1502Pam/Project/Imágenes/2B.png

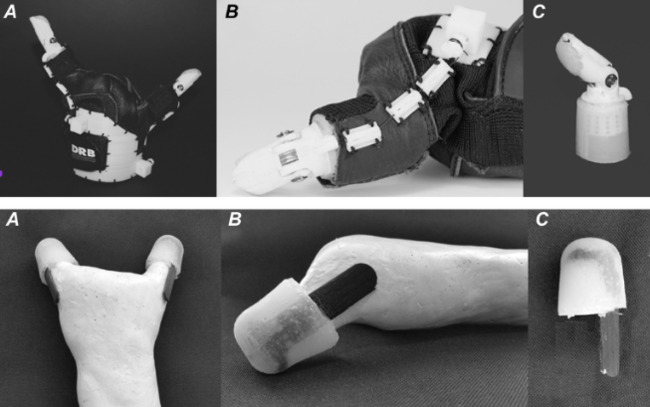
Imágenes/2B.png
