1502Pam/Project/Imágenes/1M_n.jpeg

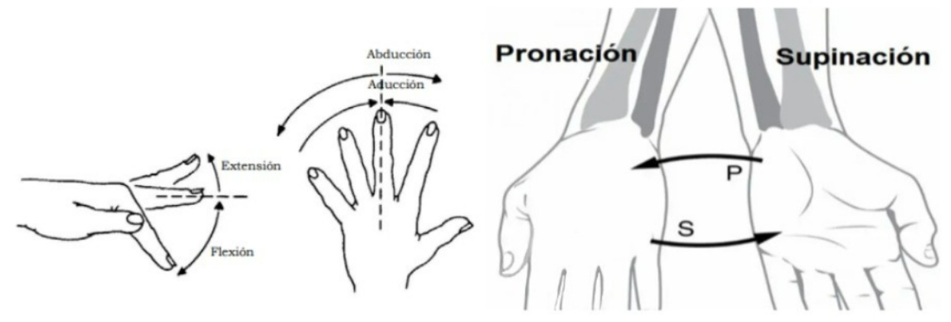
Imágenes/1M_n.jpeg
