1502Pam/Project/Imágenes/1S.jpg

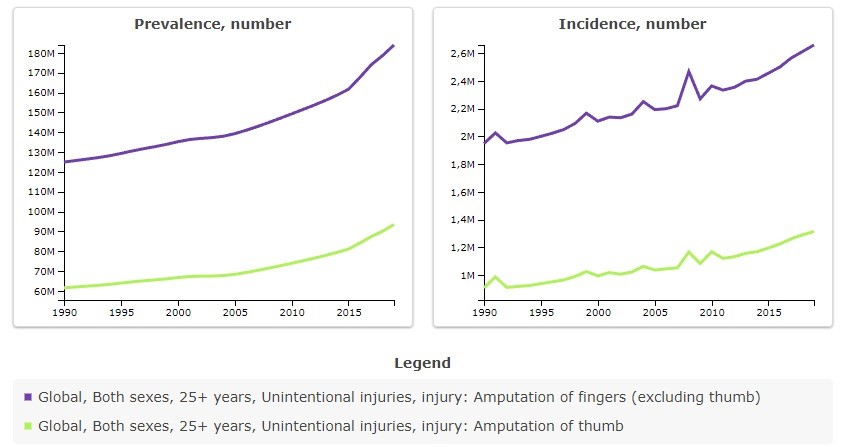
Imágenes/1S.jpg
