1502Pam/Project/Imágenes/3M_n.jpeg

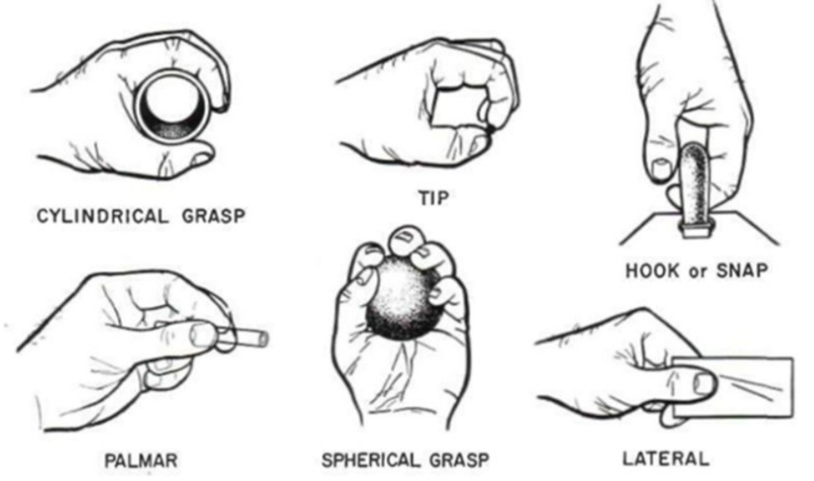
Imágenes/3M_n.jpeg
