1502Pam/Project/Imágenes/4B.png

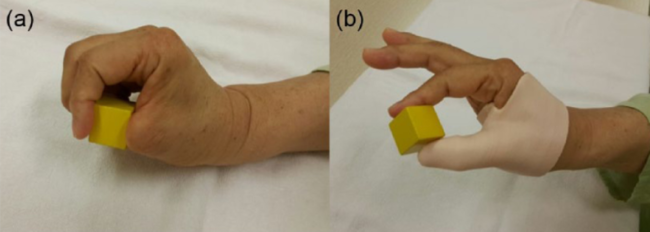
Imágenes/4B.png
