1502Pam/Project/Imágenes/10_2023-08-31 125352.jpg

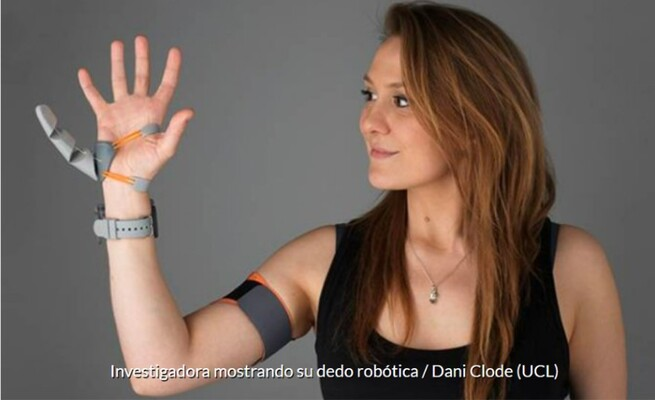
Imágenes/10_2023-08-31 125352.jpg
