1502Pam/Project/Imágenes/B1.png

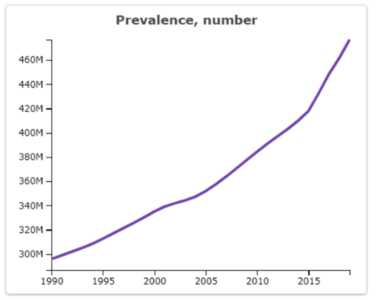
Imágenes/B1.png
