1502Pam/Project/Imágenes/B2.png

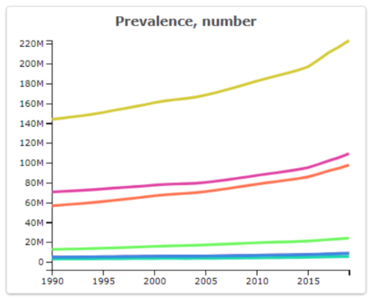
Imágenes/B2.png
