1502Pam/Project/Imágenes/B3.png

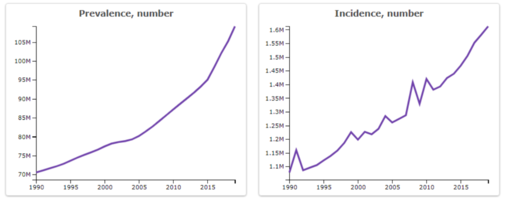
Imágenes/B3.png
