1502Pam/Project/Imágenes/B5.png

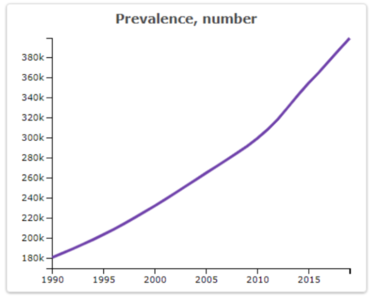
Imágenes/B5.png
