1502Pam/Project/Imágenes/boceto3.1.jpg

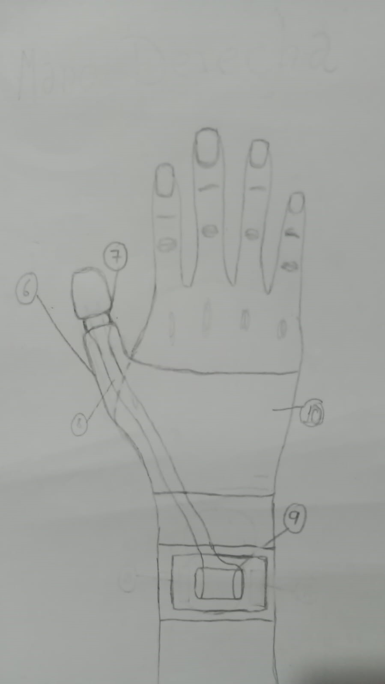
Imágenes/boceto3.1.jpg
