1502Pam/Project/Imágenes/boceto3.jpg

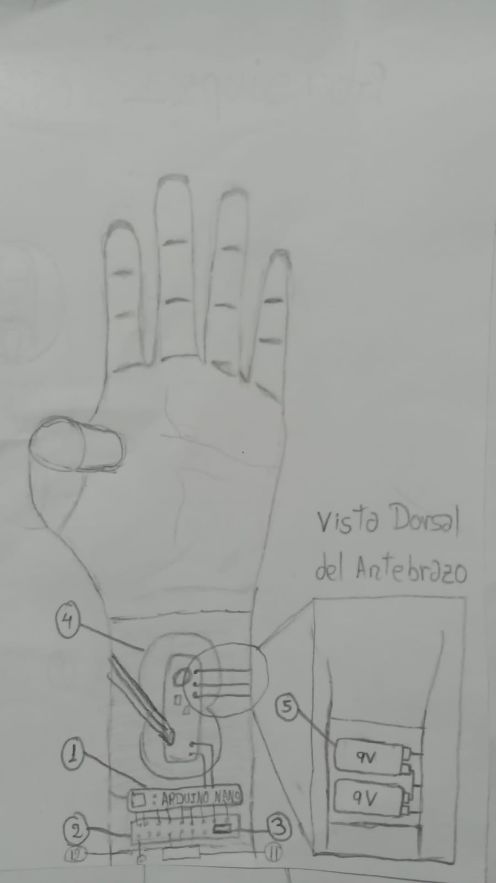
Imágenes/boceto3.jpg
