1502Pam/Project/Imágenes/boceto_1.1.png

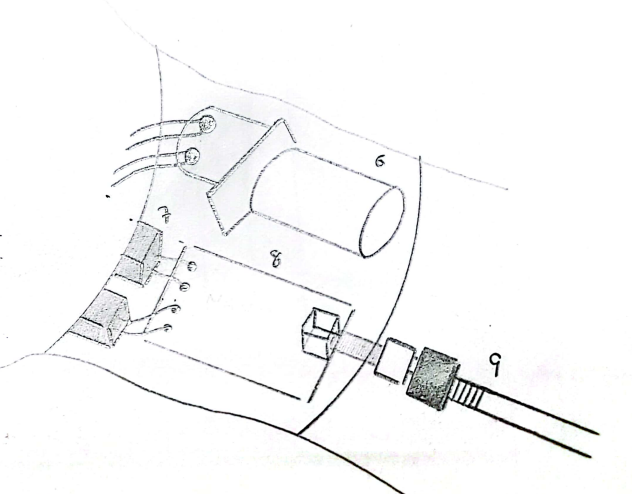
Imágenes/boceto_1.1.png
