1502Pam/Project/Imágenes/boceto_1.png

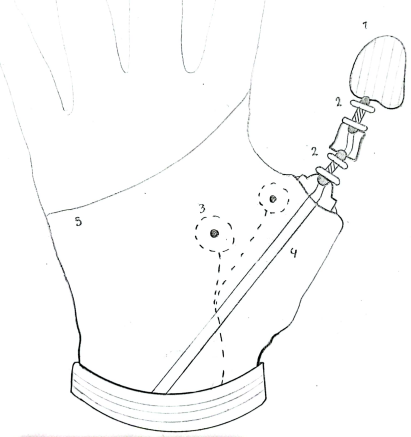
Imágenes/boceto_1.png
