1502Pam/Project/Imágenes/boceto_2.jpg

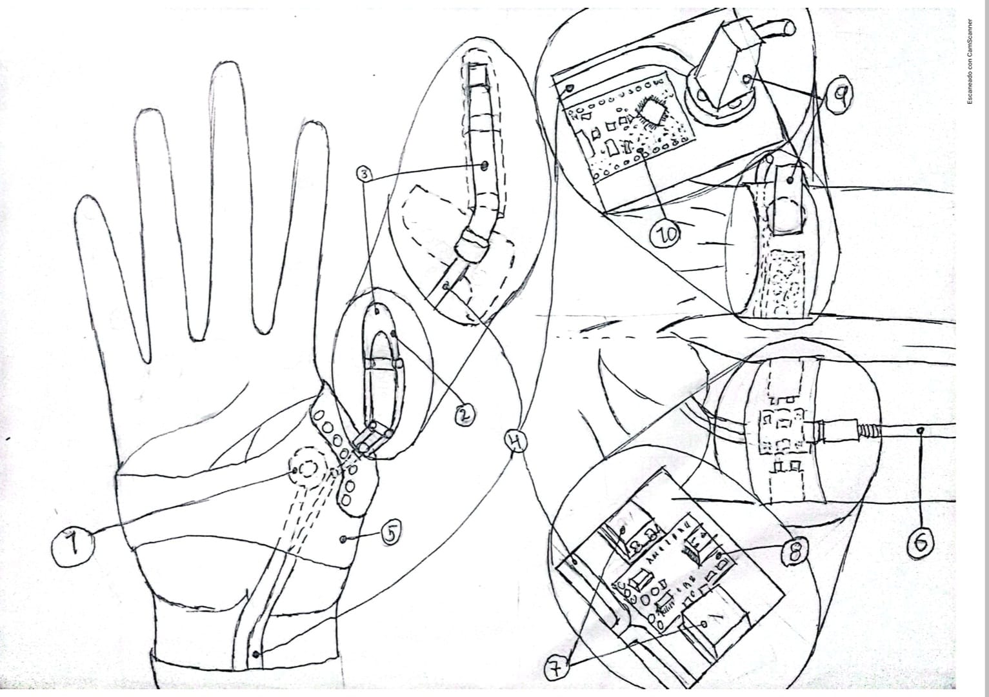
Imágenes/boceto_2.jpg
