1502Pam/Project/Imágenes/caja_negra.jpeg

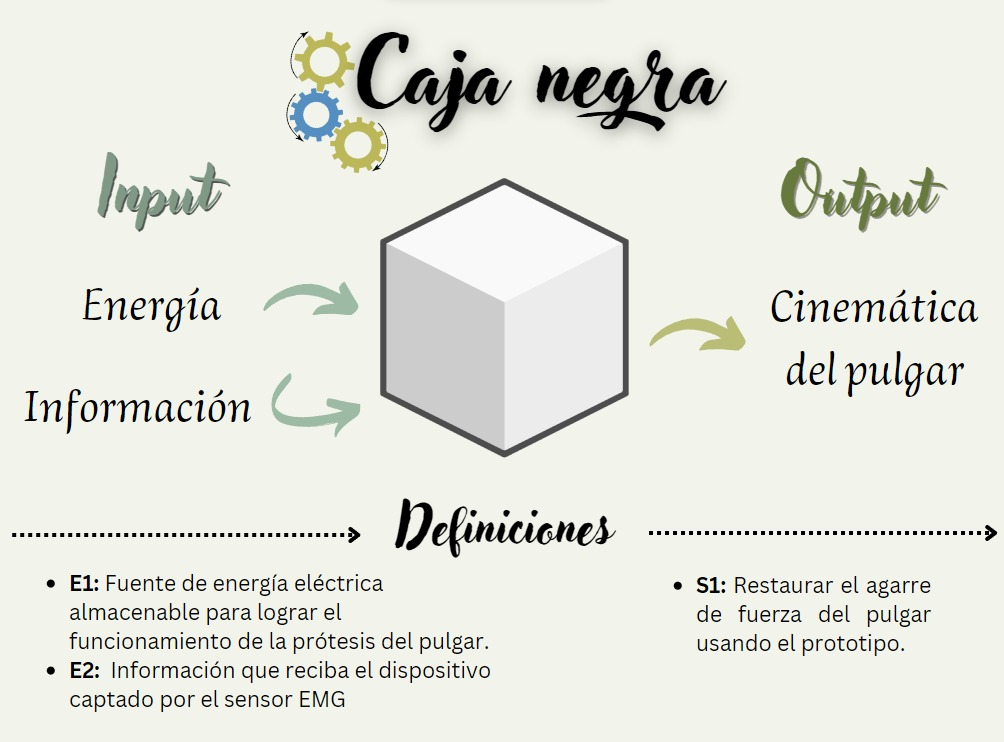
Imágenes/caja_negra.jpeg
