1502Pam/Project/Imágenes/carcasa 1.1V.jpeg

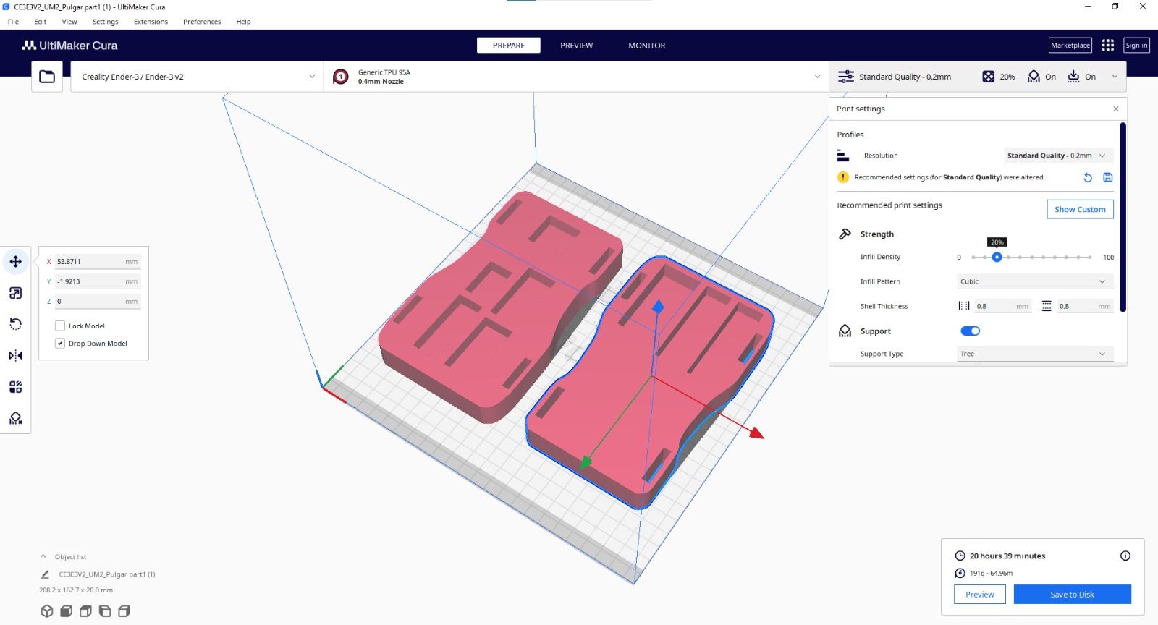
Imágenes/carcasa 1.1V.jpeg
