1502Pam/Project/Imágenes/carcasa 1.2V.jpeg

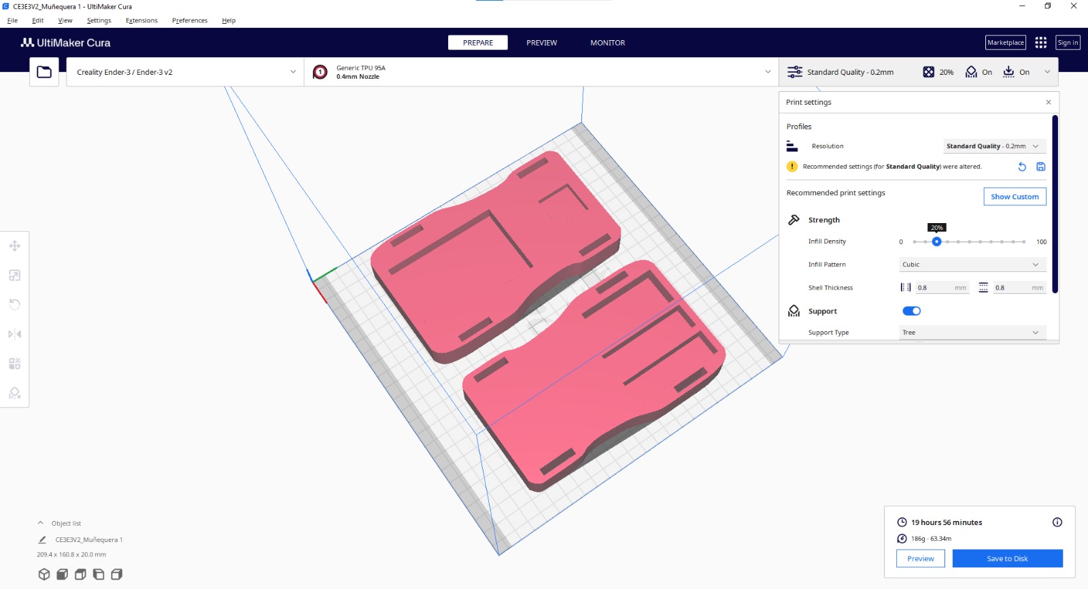
Imágenes/carcasa 1.2V.jpeg
