1502Pam/Project/Imágenes/codigo_EMG1_act.jpeg

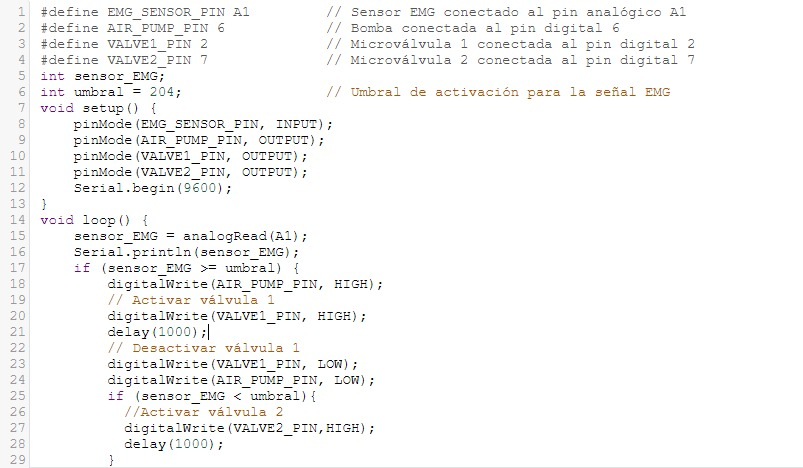
Imágenes/codigo_EMG1_act.jpeg
