1502Pam/Project/Imágenes/código_sensorFSR.jpeg

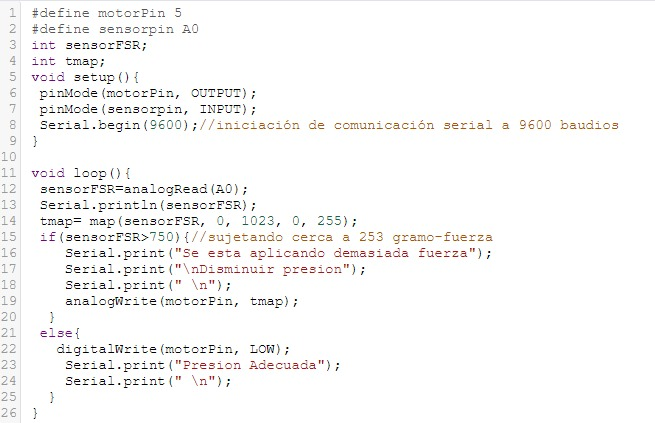
Imágenes/código_sensorFSR.jpeg
