1502Pam/Project/Imágenes/Despiece2.jpg

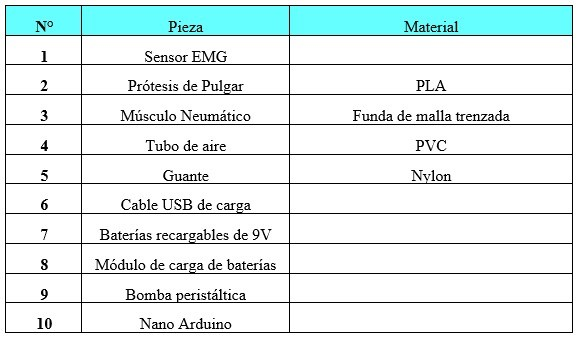
Imágenes/Despiece2.jpg
