1502Pam/Project/Imágenes/despiece3.jpg

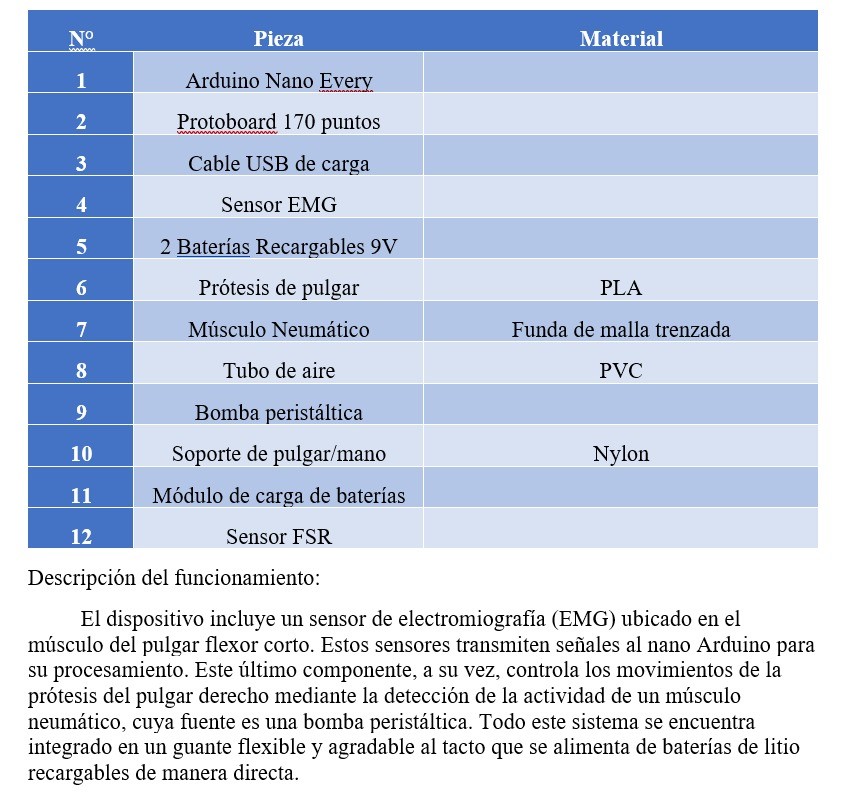
Imágenes/despiece3.jpg
