1502Pam/Project/Imágenes/Despiece_1.1.png

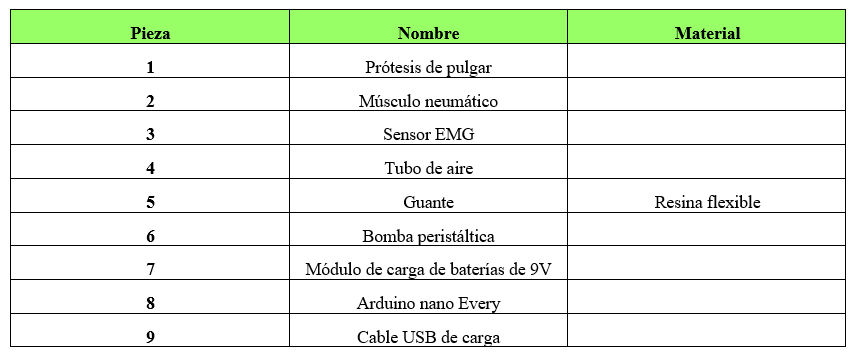
Imágenes/Despiece_1.1.png
