1502Pam/Project/Imágenes/dos_pulgares.png

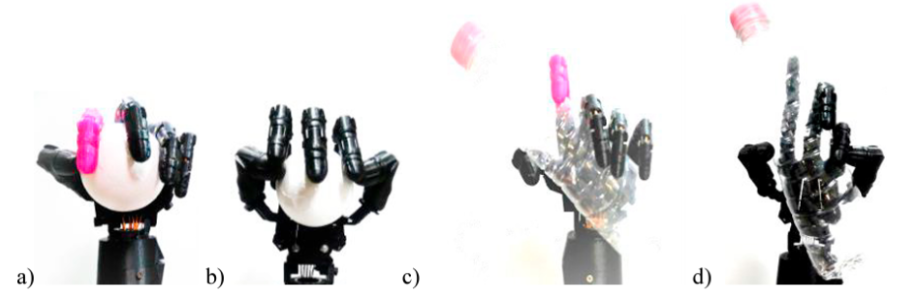
Imágenes/dos_pulgares.png
