1502Pam/Project/Imágenes/esquema_funciones.jpeg

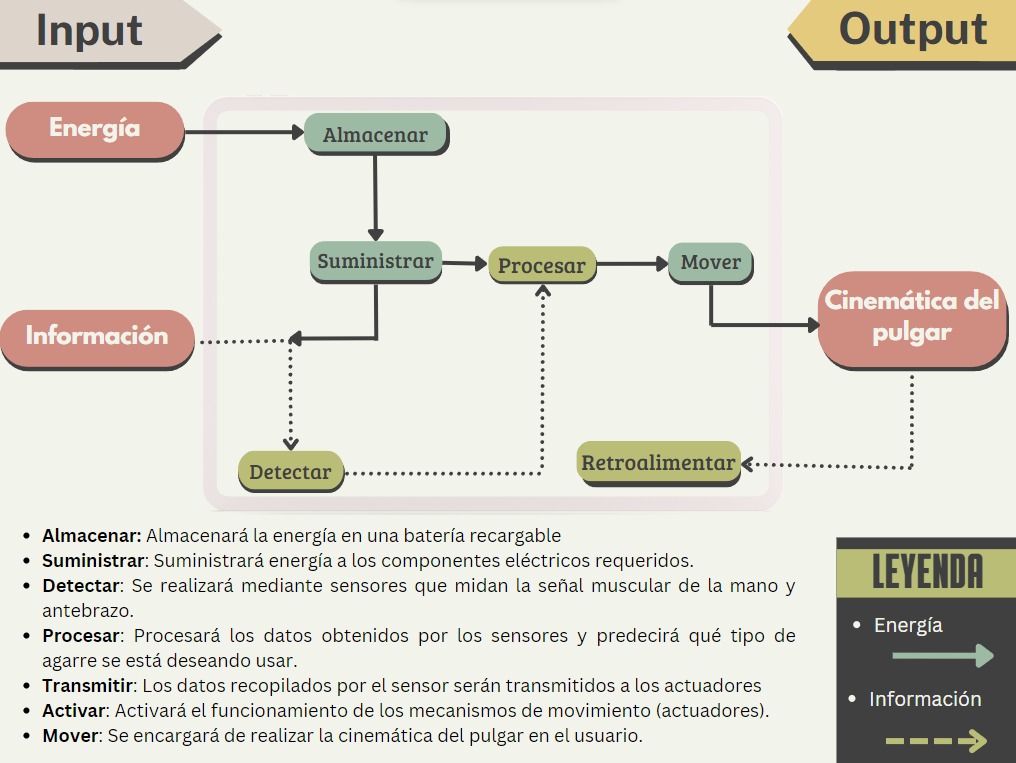
Imágenes/esquema_funciones.jpeg
