1502Pam/Project/Imágenes/evaluación_económica.jpeg

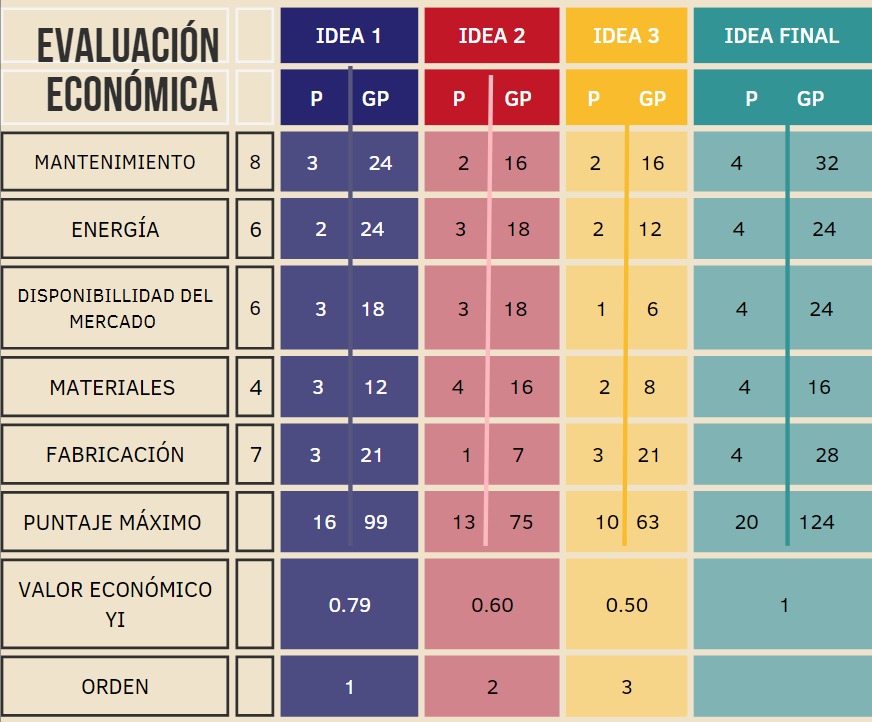
Imágenes/evaluación_económica.jpeg
