1502Pam/Project/Imágenes/flowchart .png

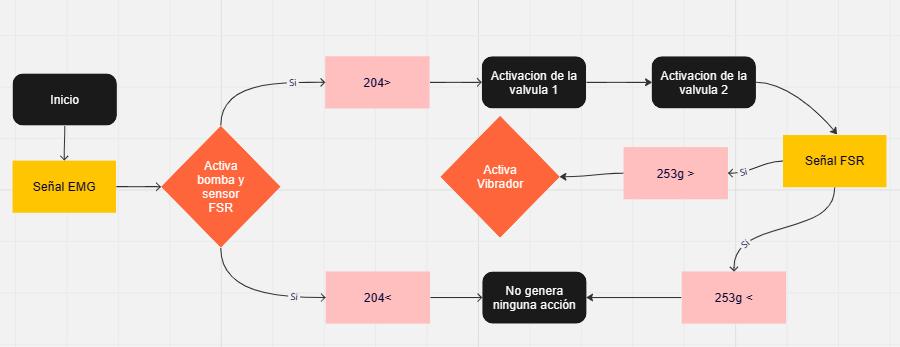
Imágenes/flowchart .png
