1502Pam/Project/Imágenes/foto_grupal_2.jpg

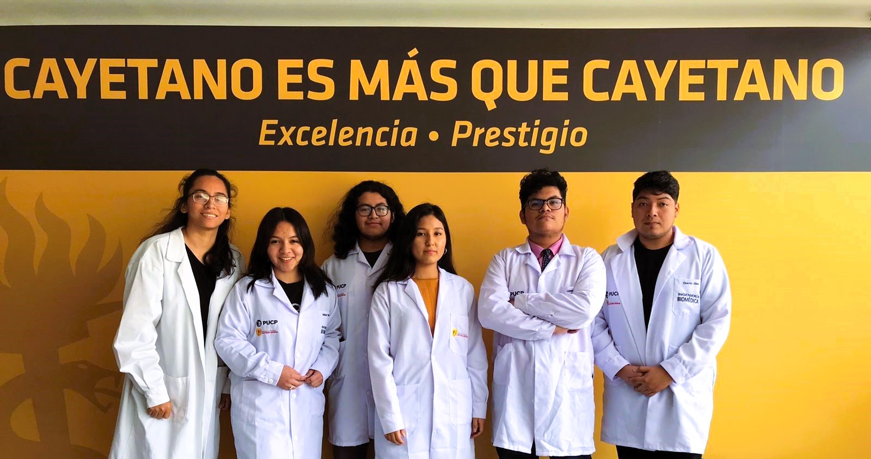
Imágenes/foto_grupal_2.jpg
