1502Pam/Project/Imágenes/grafica_proyecto_optimo.jpeg

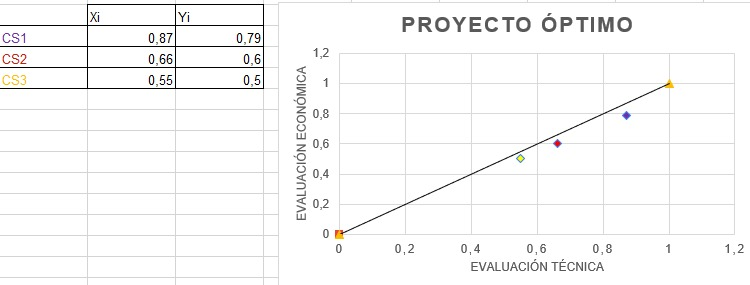
Imágenes/grafica_proyecto_optimo.jpeg
