1502Pam/Project/Imágenes/griplock.png

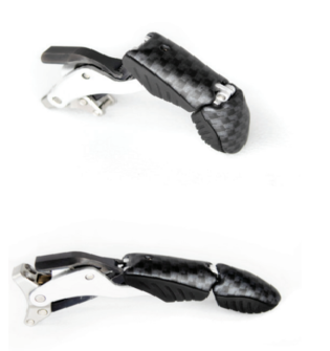
Imágenes/griplock.png
