1502Pam/Project/Imágenes/hito_1.png

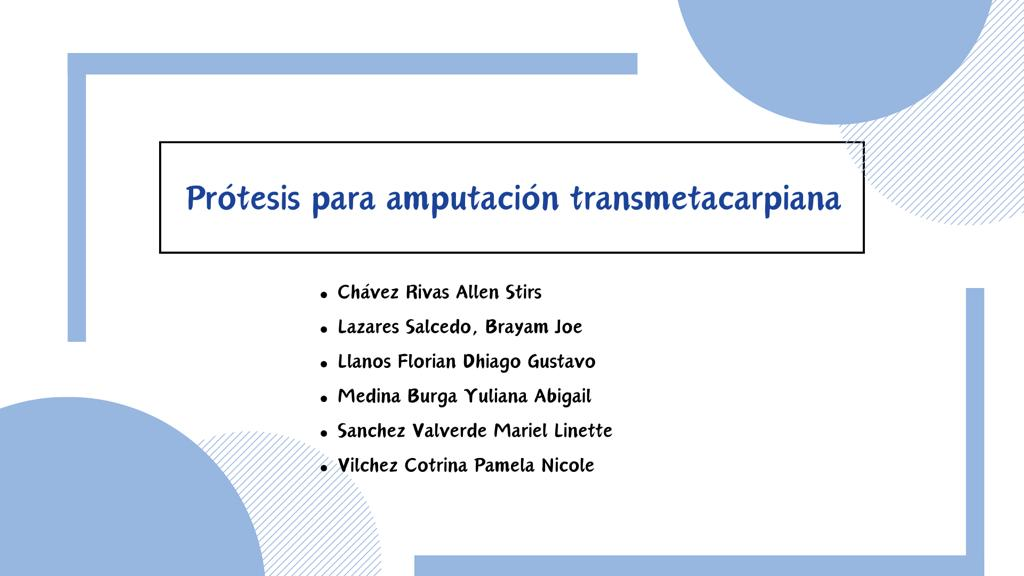
Imágenes/hito_1.png
