1502Pam/Project/Imágenes/hito_3.png

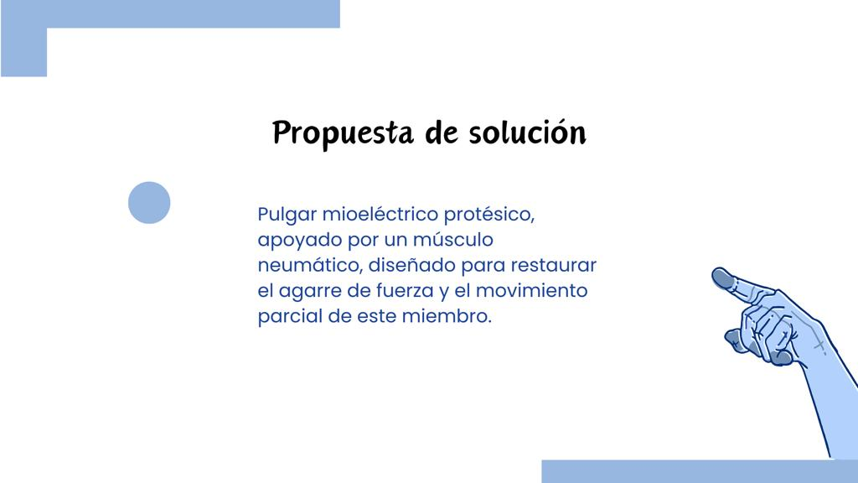
Imágenes/hito_3.png
