1502Pam/Project/Imágenes/hito_5.png

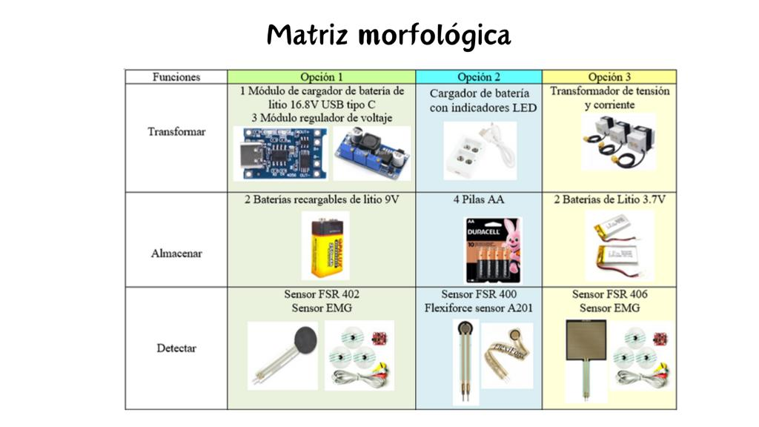
Imágenes/hito_5.png
