1502Pam/Project/Imágenes/hito_6.png

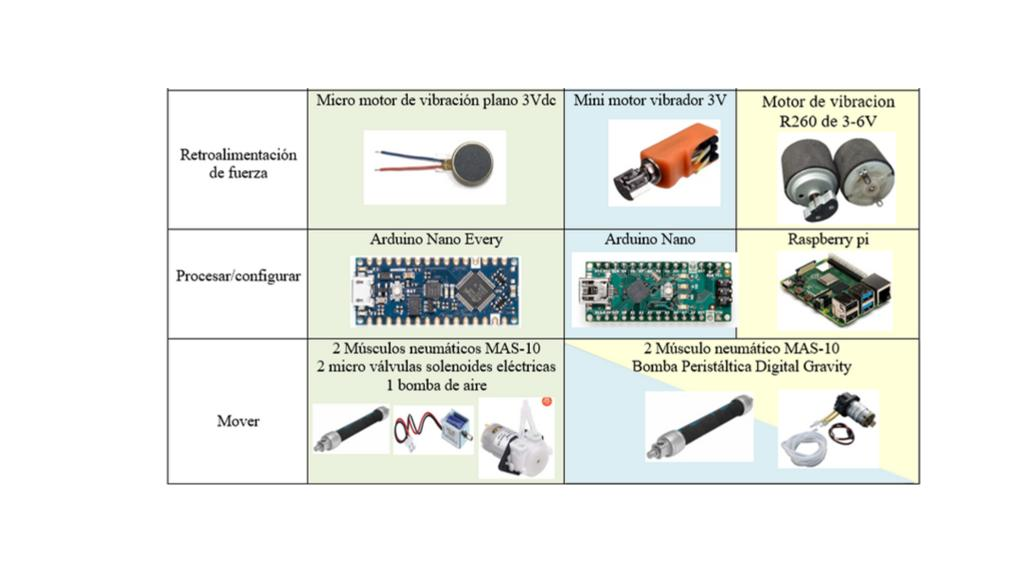
Imágenes/hito_6.png
