1502Pam/Project/Imágenes/hito_7.jpeg

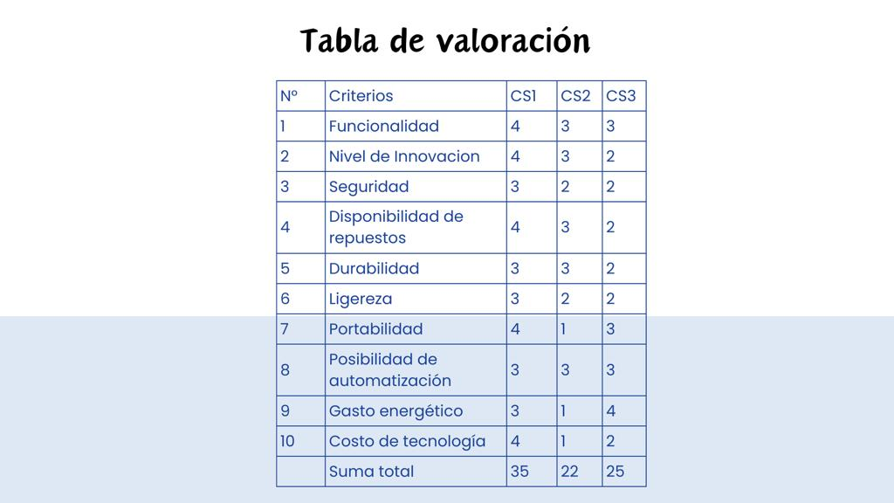
Imágenes/hito_7.jpeg
