1502Pam/Project/Imágenes/hito_8.png

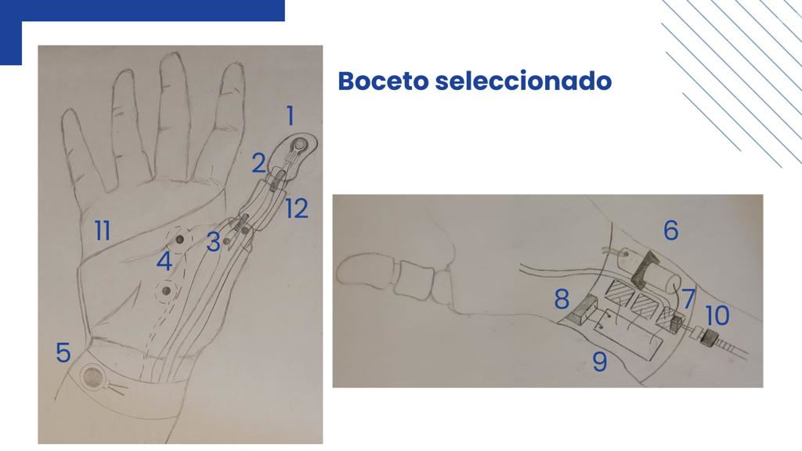
Imágenes/hito_8.png
