1502Pam/Project/Imágenes/hito_10.png

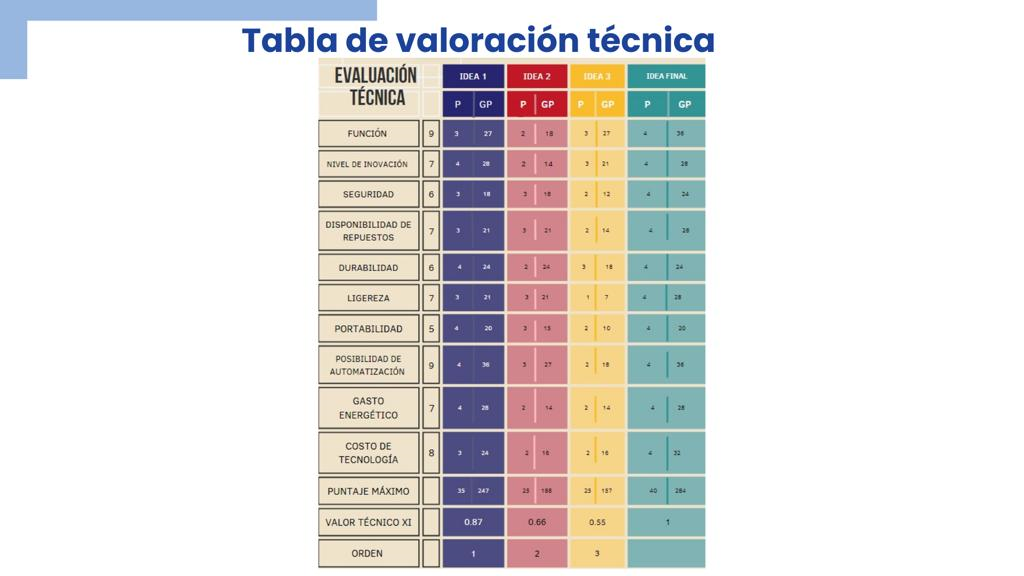
Imágenes/hito_10.png
