1502Pam/Project/Imágenes/hito_11.png

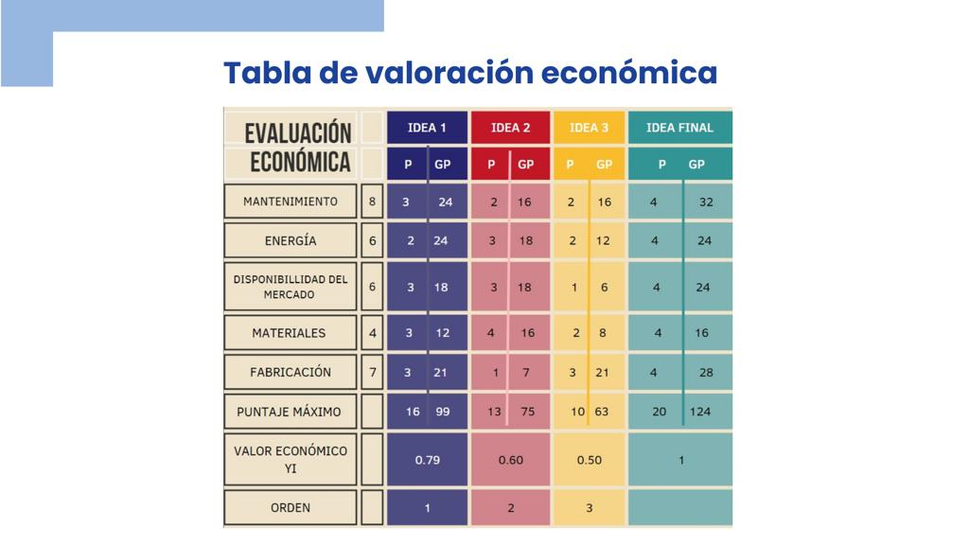
Imágenes/hito_11.png
