1502Pam/Project/Imágenes/hito_12.png

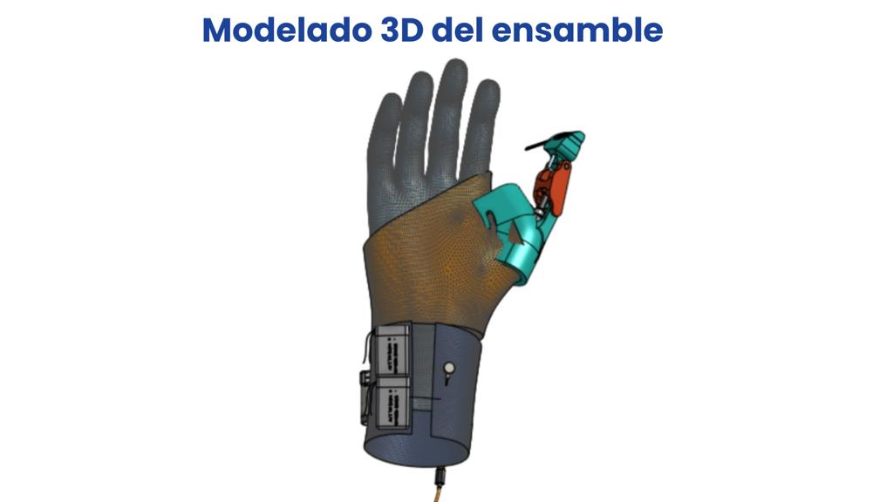
Imágenes/hito_12.png
