1502Pam/Project/Imágenes/hito_13.png

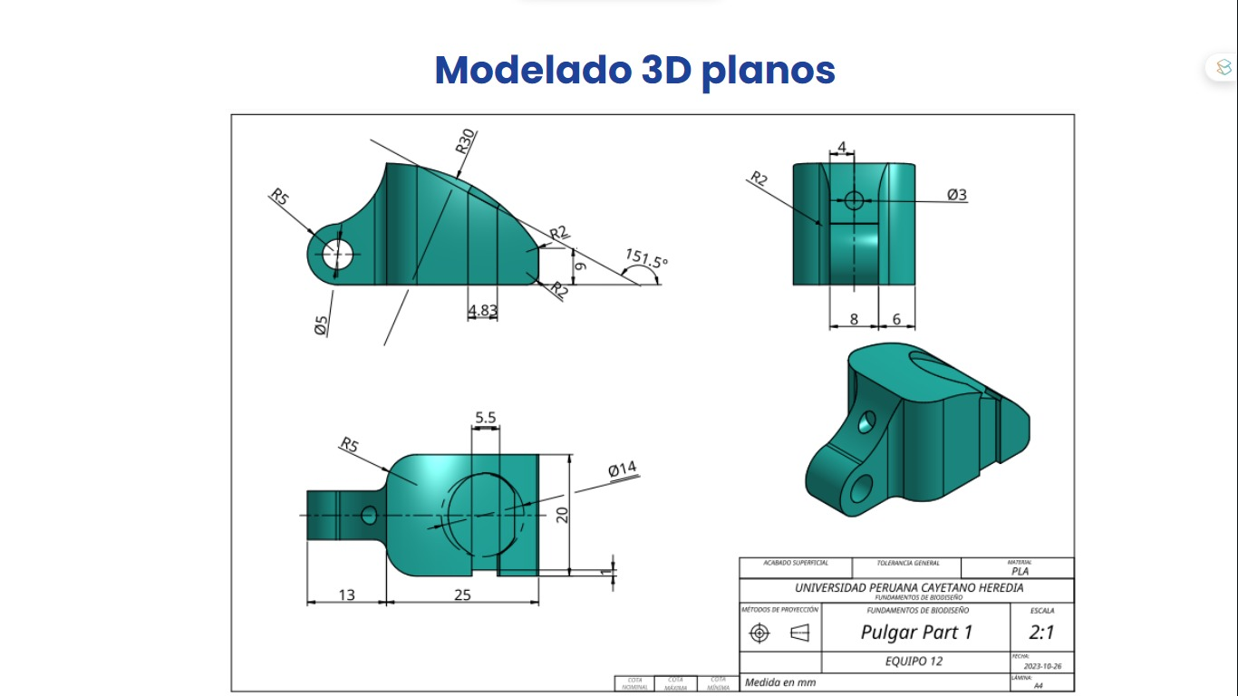
Imágenes/hito_13.png
