1502Pam/Project/Imágenes/hito_14.png

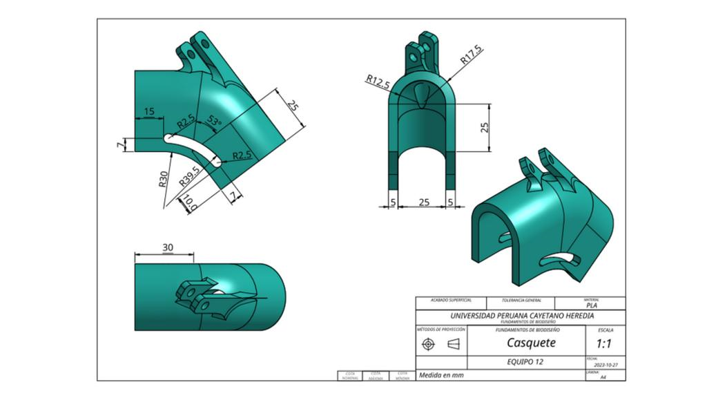
Imágenes/hito_14.png
