1502Pam/Project/Imágenes/hito_15.png

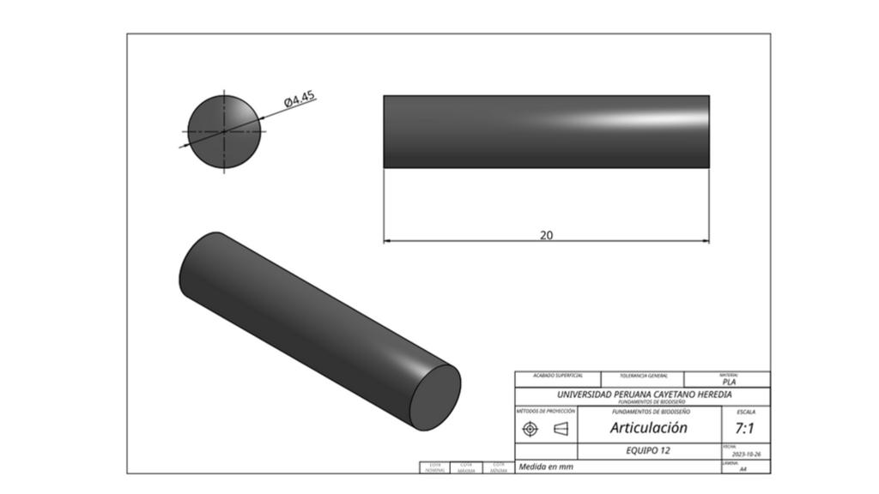
Imágenes/hito_15.png
