1502Pam/Project/Imágenes/hito_16.png

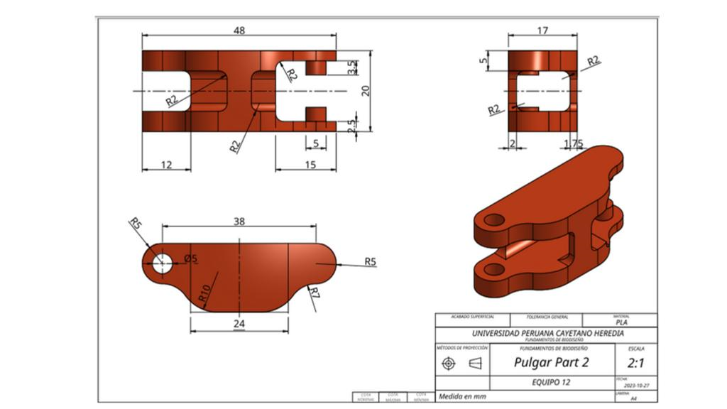
Imágenes/hito_16.png
