1502Pam/Project/Imágenes/hito_17.png

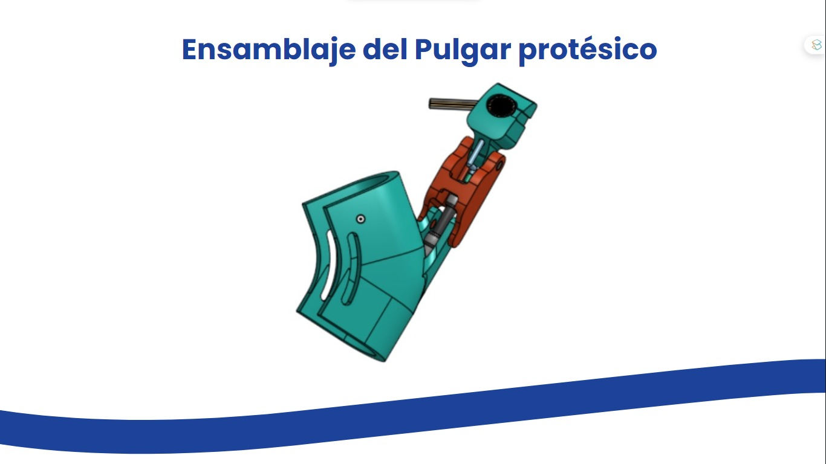
Imágenes/hito_17.png
