1502Pam/Project/Imágenes/hito_18.png

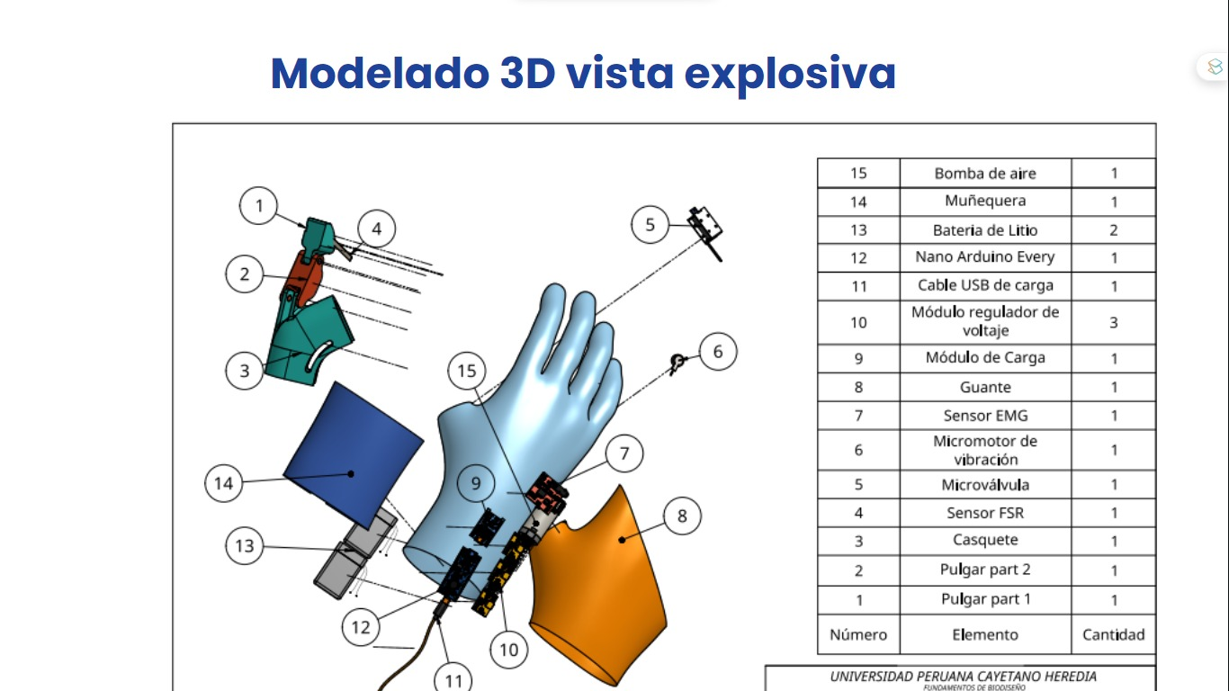
Imágenes/hito_18.png
