1502Pam/Project/Imágenes/Imagen1.png

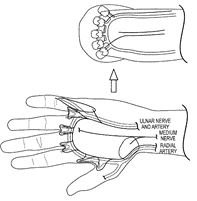
Imágenes/Imagen1.png
