1502Pam/Project/Imágenes/Imagen2.png

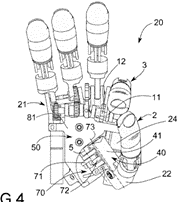
Imágenes/Imagen2.png
