1502Pam/Project/Imágenes/Imagen3.png

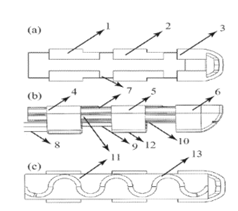
Imágenes/Imagen3.png
