1502Pam/Project/Imágenes/Imagen4.png

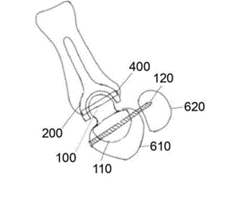
Imágenes/Imagen4.png
