1502Pam/Project/Imágenes/matriz_3.png

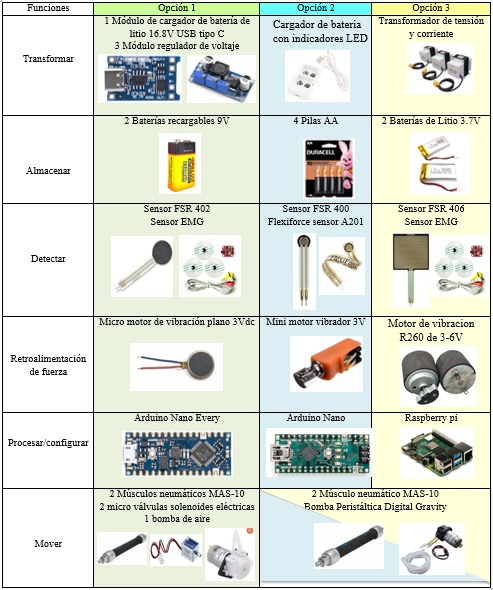
Imágenes/matriz_3.png
