1502Pam/Project/Imágenes/now.jpeg

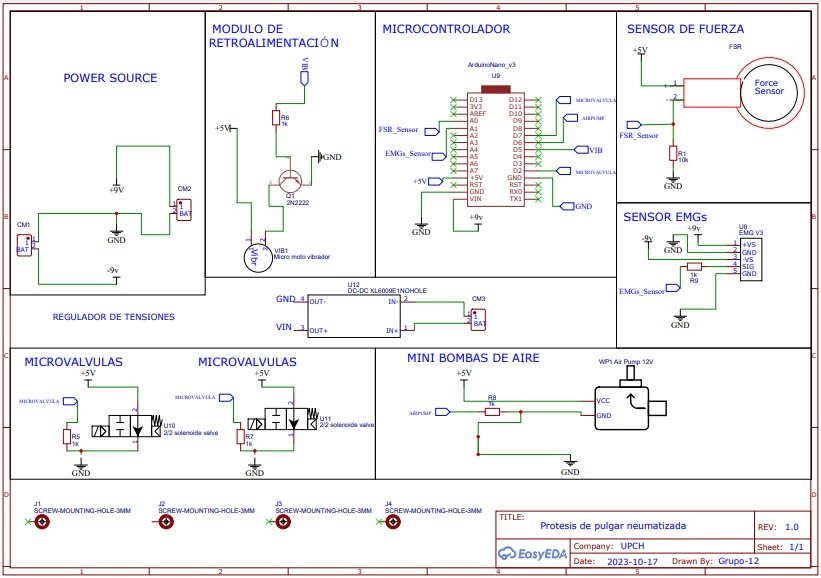
Imágenes/now.jpeg
