1502Pam/Project/Imágenes/PIPdriver.png

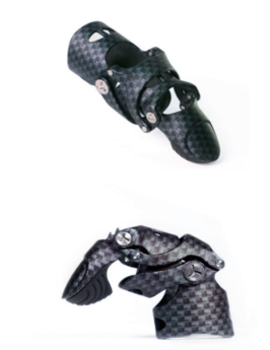
Imágenes/PIPdriver.png
