1502Pam/Project/Imágenes/protesis_mioeléctrica.png

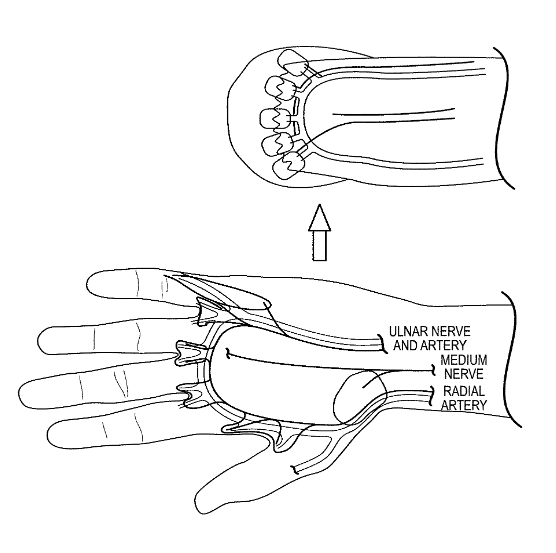
Imágenes/protesis_mioeléctrica.png
