1502Pam/Project/Imágenes/protesis_multifuncional.png

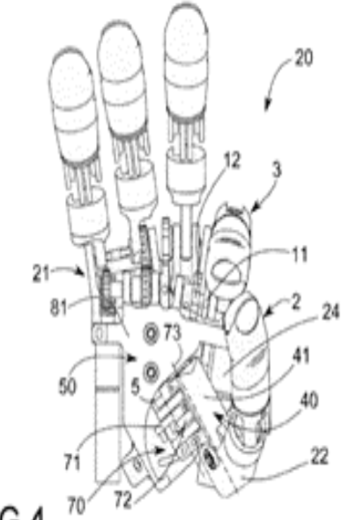
Imágenes/protesis_multifuncional.png
