1502Pam/Project/Imágenes/protesis_trans.png

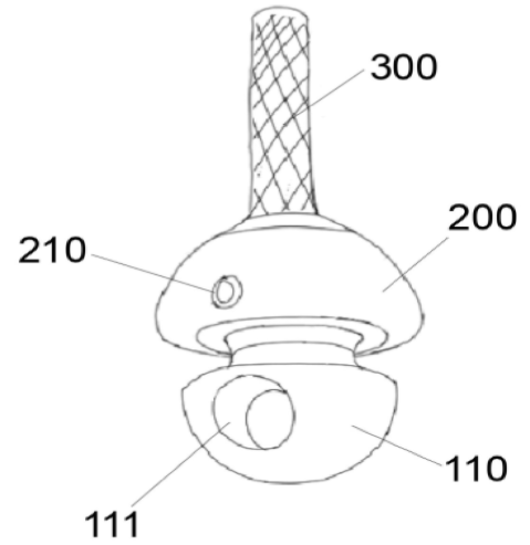
Imágenes/protesis_trans.png
