1502Pam/Project/Imágenes/pulgar_protésico.jpeg

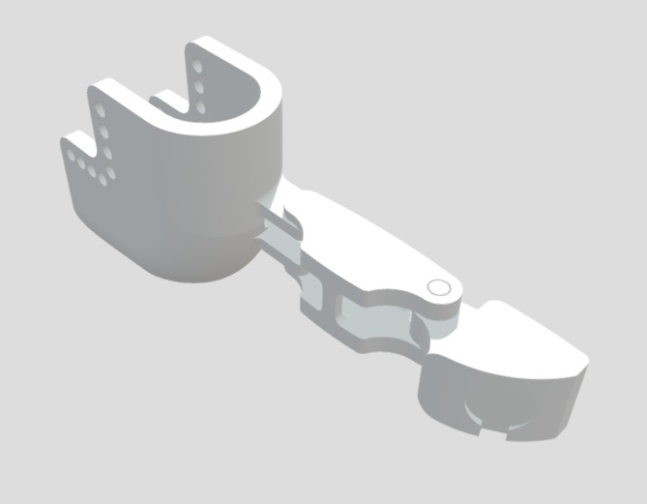
Imágenes/pulgar_protésico.jpeg
