1502Pam/Project/Imágenes/R1.jpg

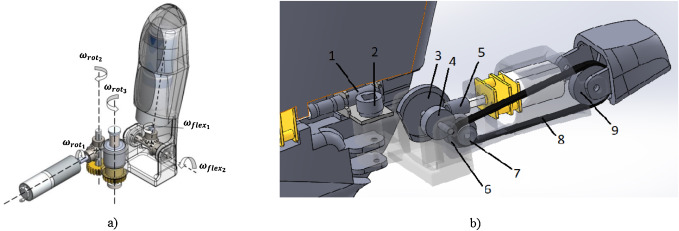
Imágenes/R1.jpg
