1502Pam/Project/Imágenes/R2.jpg

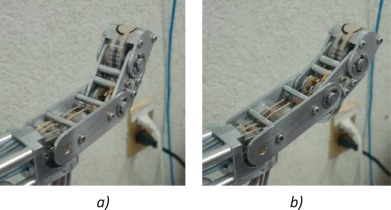
Imágenes/R2.jpg
