1502Pam/Project/Imágenes/R3.jpg

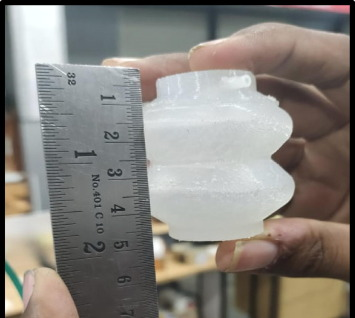
Imágenes/R3.jpg
