1502Pam/Project/Imágenes/soporte_de_antebrazo.jpeg

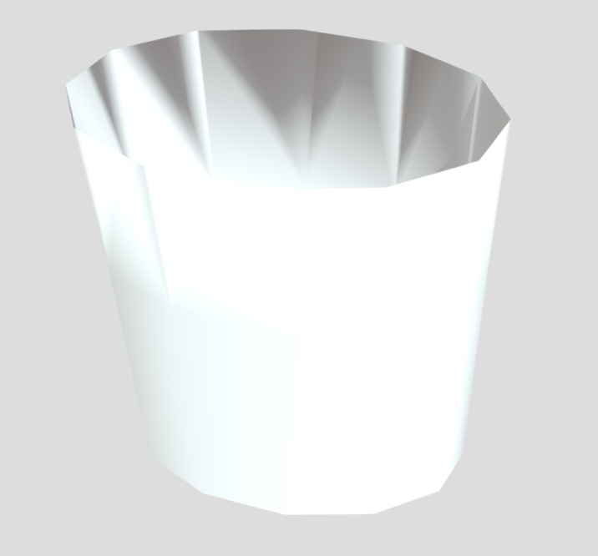
Imágenes/soporte_de_antebrazo.jpeg
