1502Pam/Project/Imágenes/soporte_pulgar.jpeg

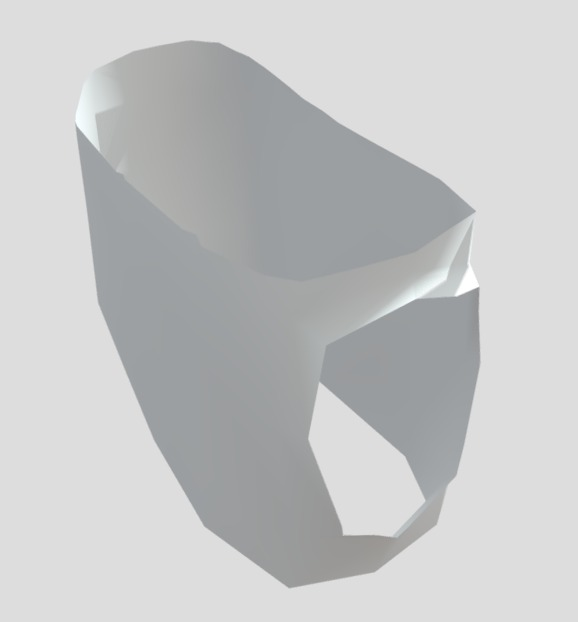
Imágenes/soporte_pulgar.jpeg
