1502Pam/Project/Imágenes/tabla_3.jpg

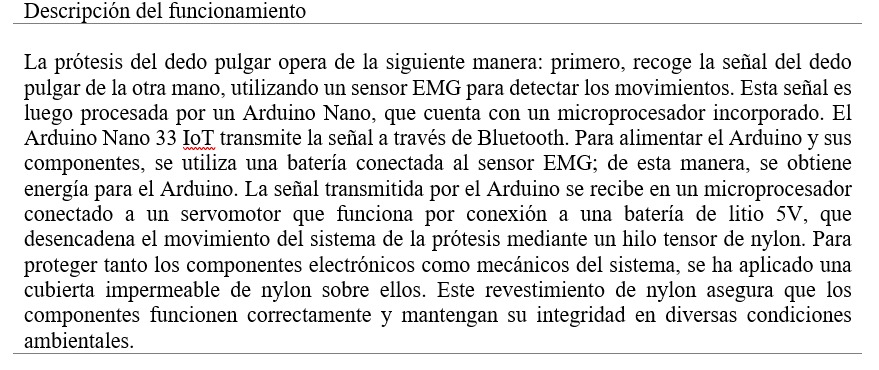
Imágenes/tabla_3.jpg
