1502Pam/Project/Imágenes/thumbdriver.png

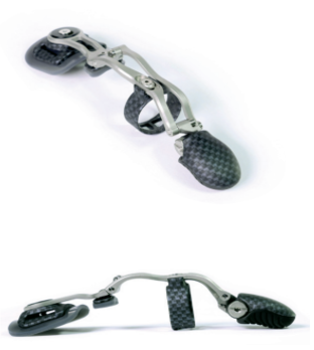
Imágenes/thumbdriver.png
