1502Pam/Project/Imágenes/tubo_de_aire.jpeg

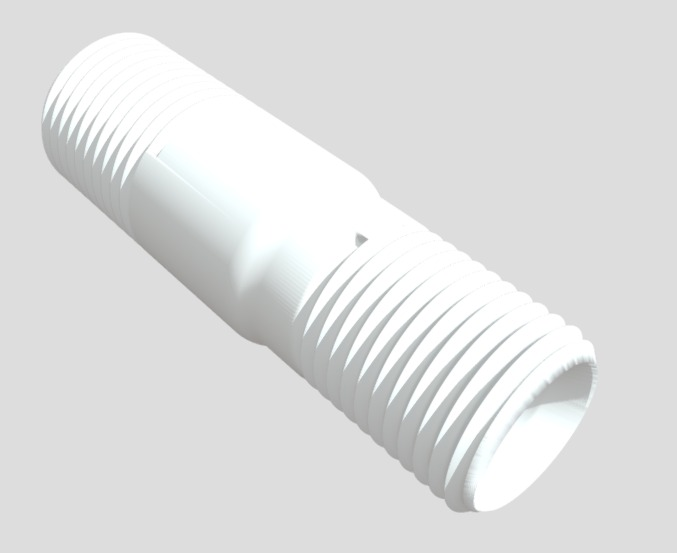
Imágenes/tubo_de_aire.jpeg
